Tecsmith/sr01-keyboard-pcb/docs/inspiration/_cases/1.jpg

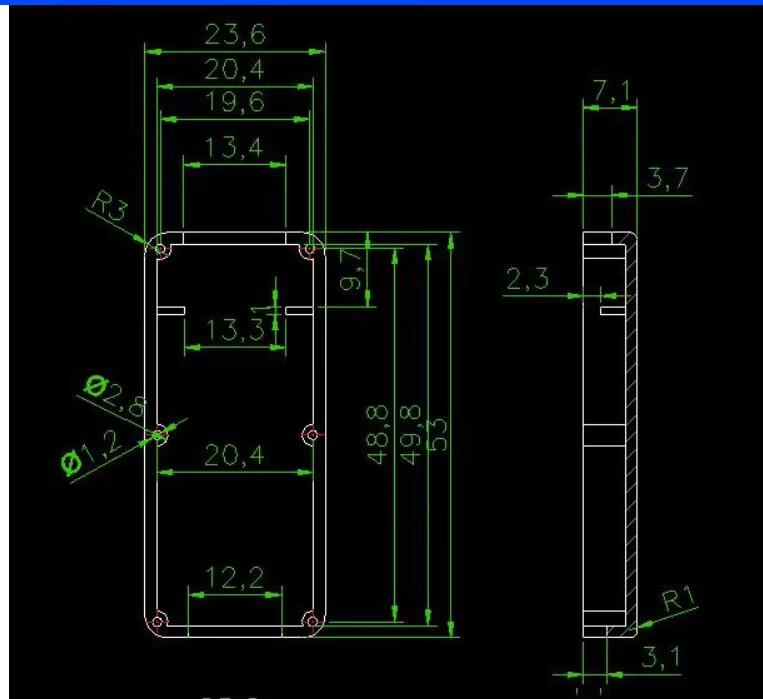
docs/inspiration/_cases/1.jpg
