Tecsmith/sr01-keyboard-pcb/docs/inspiration/_cases/2.jpg

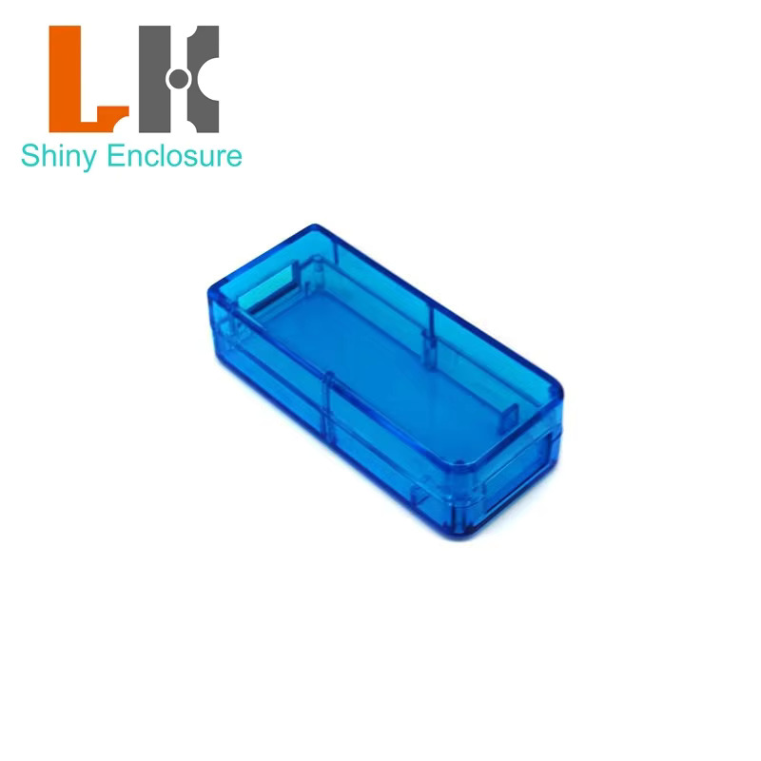
docs/inspiration/_cases/2.jpg
