Tecsmith/sr01-keyboard-pcb/docs/inspiration/cactus-whid/back.jpg

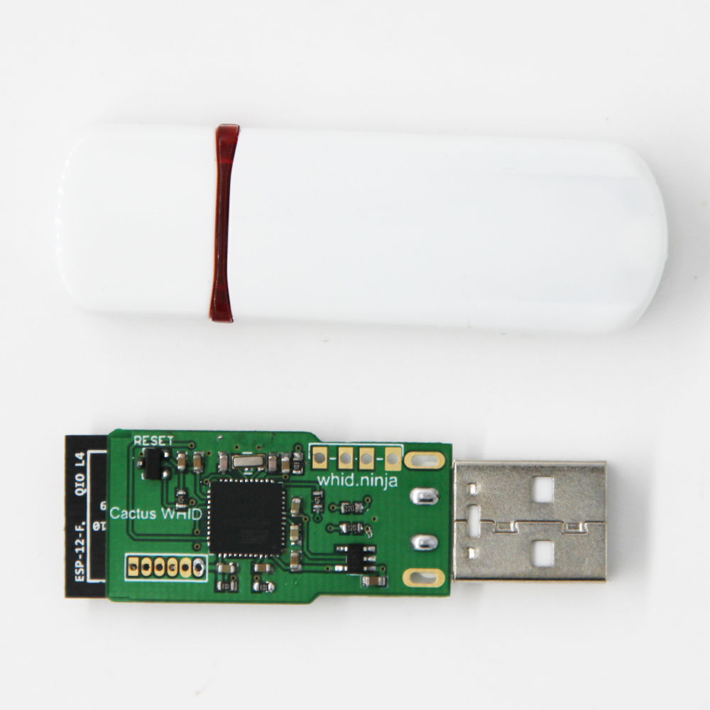
docs/inspiration/cactus-whid/back.jpg
