Tecsmith/sr01-keyboard-pcb/docs/inspiration/digispark/digispark_digistump.png

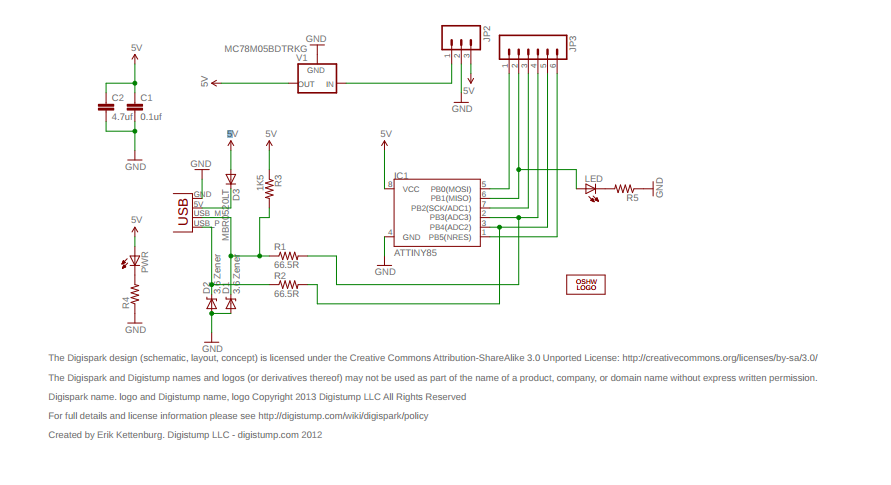
docs/inspiration/digispark/digispark_digistump.png
