Tecsmith/sr01-keyboard-pcb/docs/inspiration/neokey-trinkey/5020-00.jpg

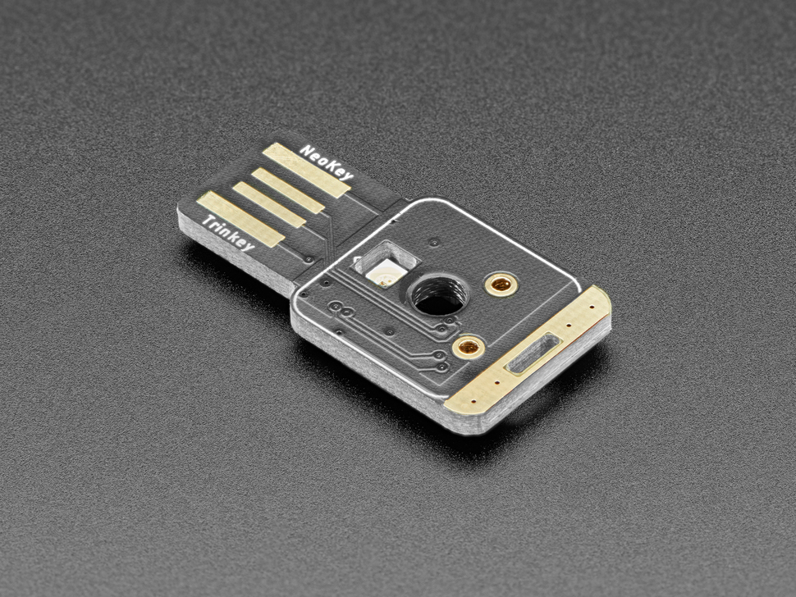
docs/inspiration/neokey-trinkey/5020-00.jpg
