Tecsmith/sr01-keyboard-pcb/docs/inspiration/neokey-trinkey/5020-01.jpg

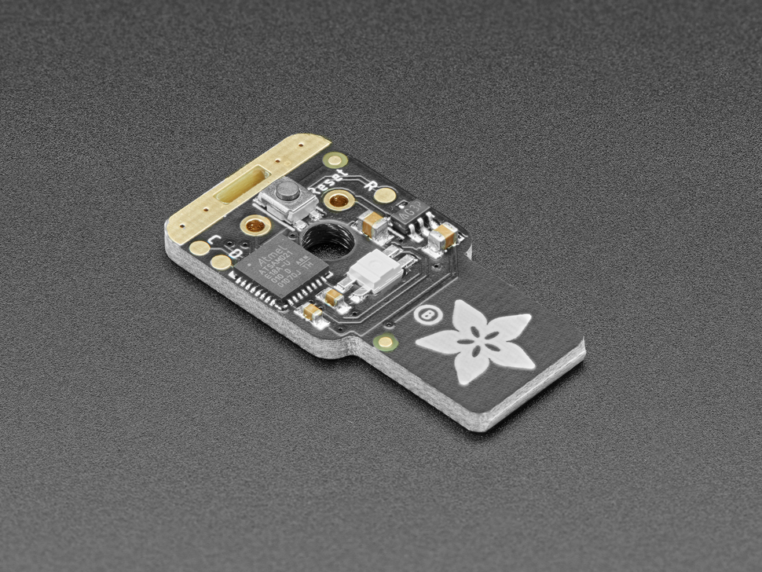
docs/inspiration/neokey-trinkey/5020-01.jpg
