Tecsmith/sr01-keyboard-pcb/docs/inspiration/neokey-trinkey/5020-03.jpg

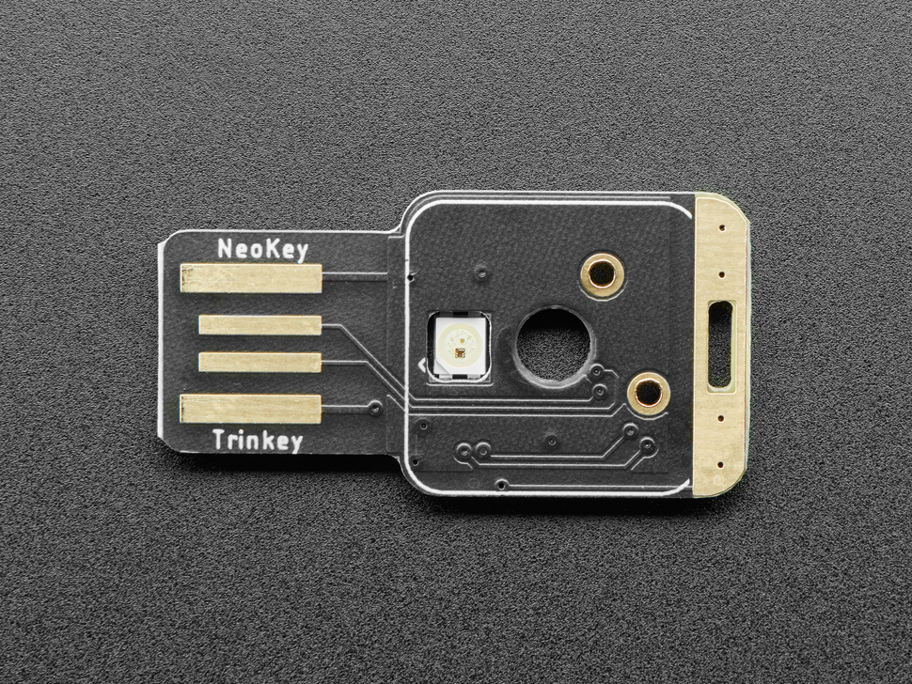
docs/inspiration/neokey-trinkey/5020-03.jpg
