Tecsmith/sr01-keyboard-pcb/docs/inspiration/neokey-trinkey/5020-05.jpg

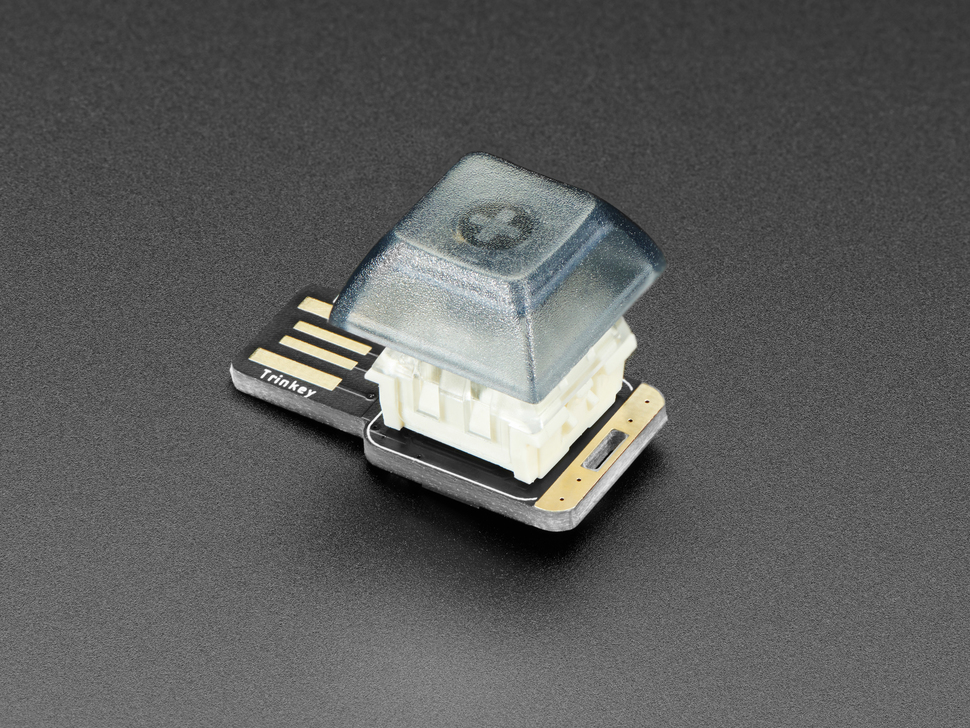
docs/inspiration/neokey-trinkey/5020-05.jpg
