Tecsmith/sr01-keyboard-pcb/docs/inspiration/neokey-trinkey/5020-08.jpg

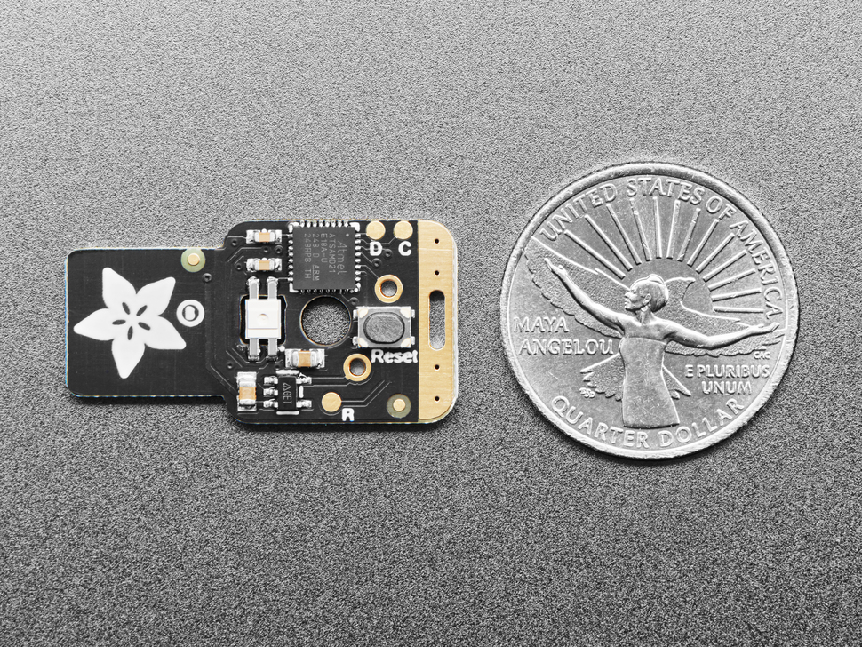
docs/inspiration/neokey-trinkey/5020-08.jpg
