Tecsmith/sr01-keyboard-pcb/docs/inspiration/snipeye-uno/uno1.jpg

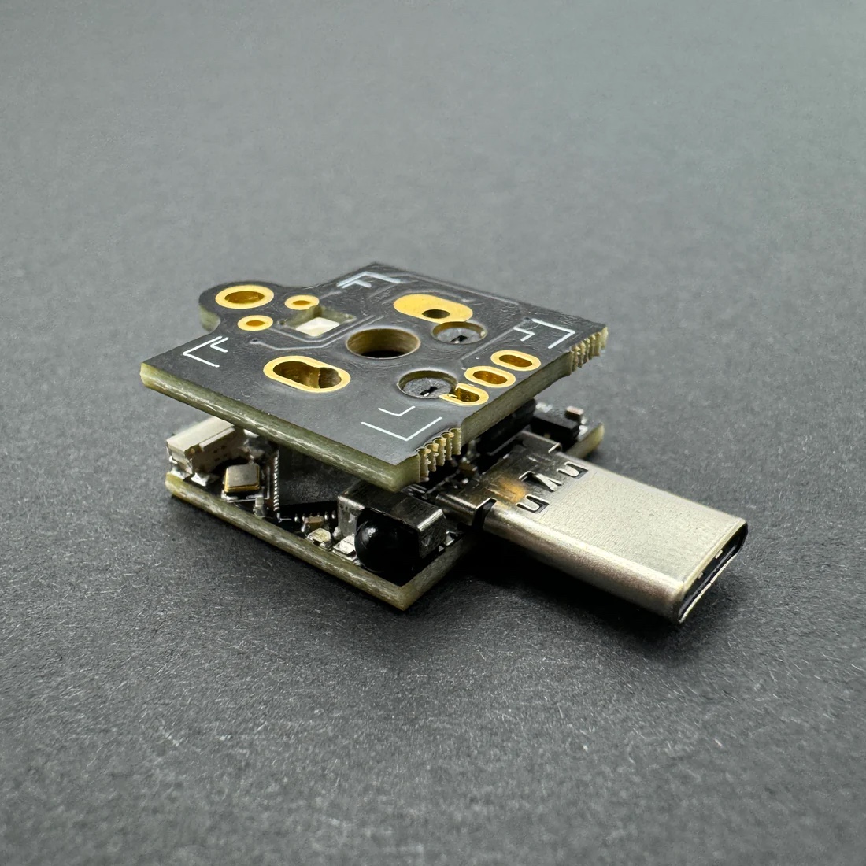
docs/inspiration/snipeye-uno/uno1.jpg
