Tecsmith/sr01-keyboard-pcb/docs/inspiration/snipeye-uno/uno3.jpg

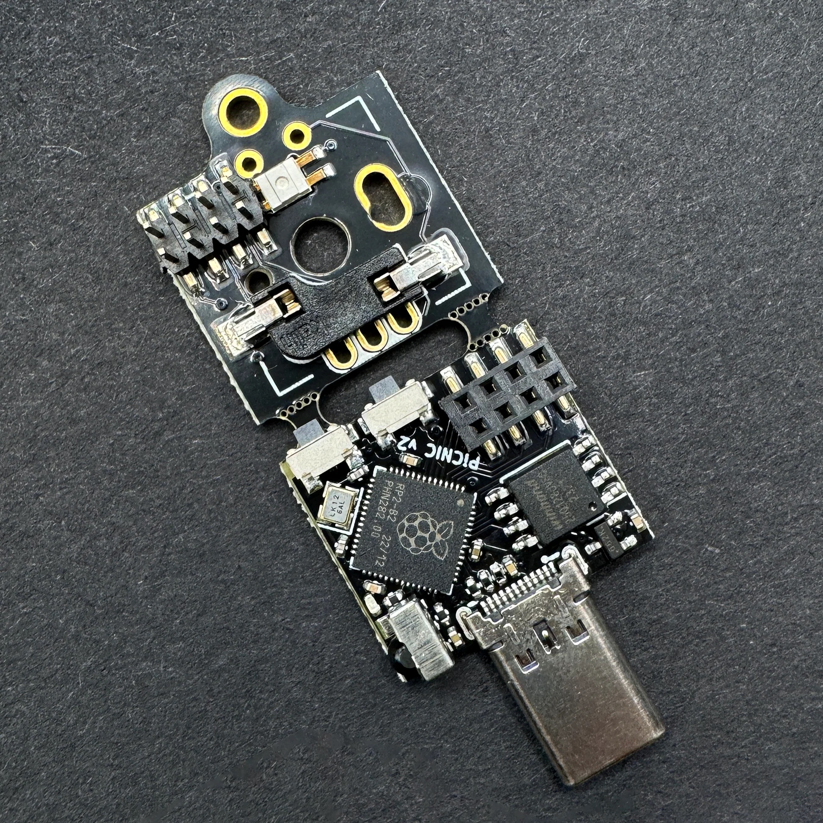
docs/inspiration/snipeye-uno/uno3.jpg
