Tecsmith/sr01-keyboard-pcb/docs/inspiration/snipeye-uno/uno4.jpg

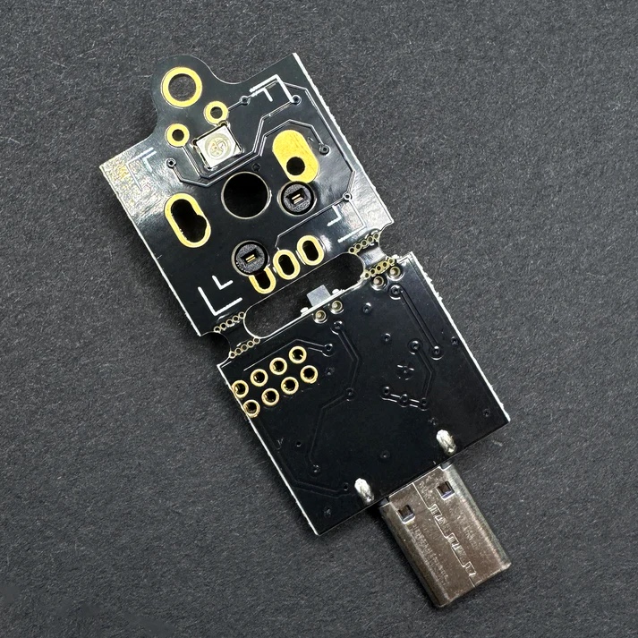
docs/inspiration/snipeye-uno/uno4.jpg
