Tecsmith/sr01-keyboard-pcb/docs/inspiration/snipeye-uno/uno5.jpg

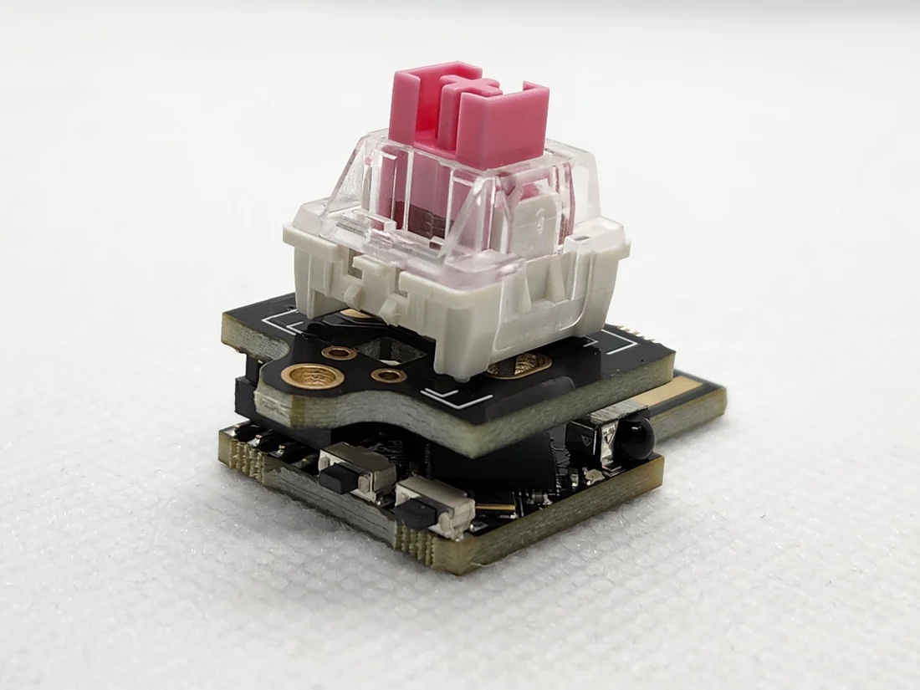
docs/inspiration/snipeye-uno/uno5.jpg
