Tecsmith/sr01-keyboard-pcb/docs/inspiration/snipeye-uno/uno7.jpg

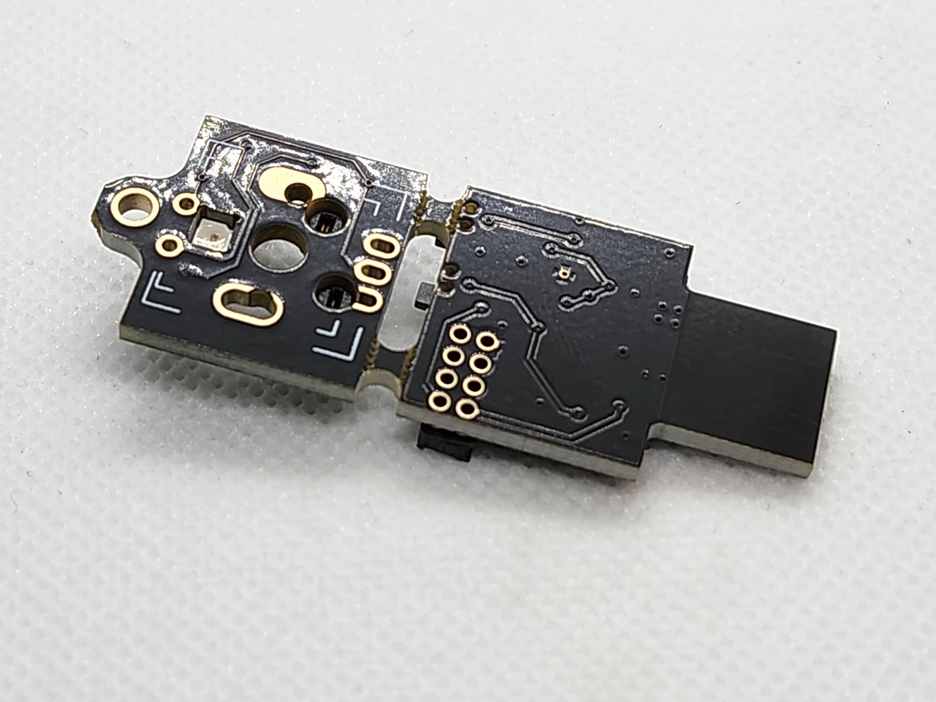
docs/inspiration/snipeye-uno/uno7.jpg
