Tecsmith/sr01-keyboard-pcb/docs/inspiration/snipeye-uno/uno9.jpg

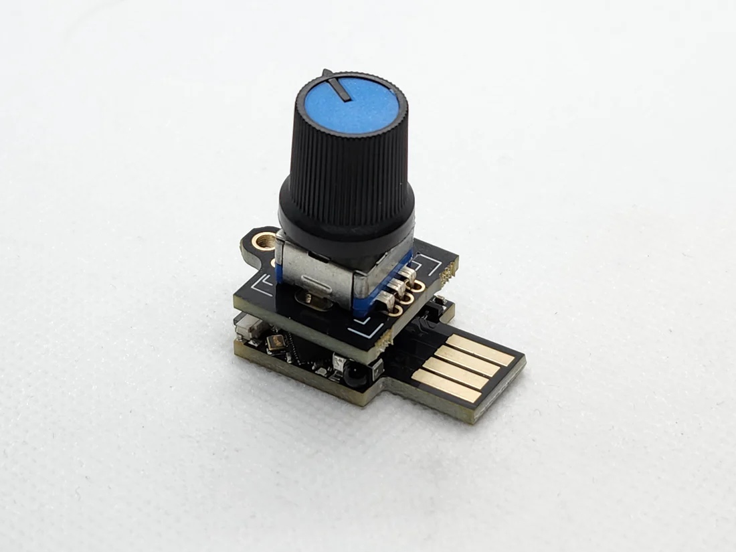
docs/inspiration/snipeye-uno/uno9.jpg
